dmitry131131/Trasser/img/1.jpg

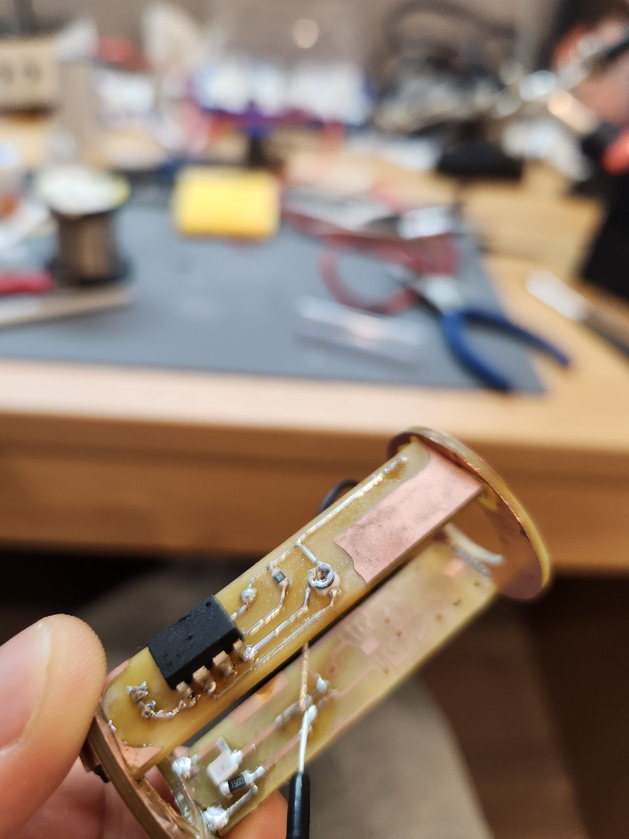
img/1.jpg
