dmitry131131/Trasser/img/2.jpg

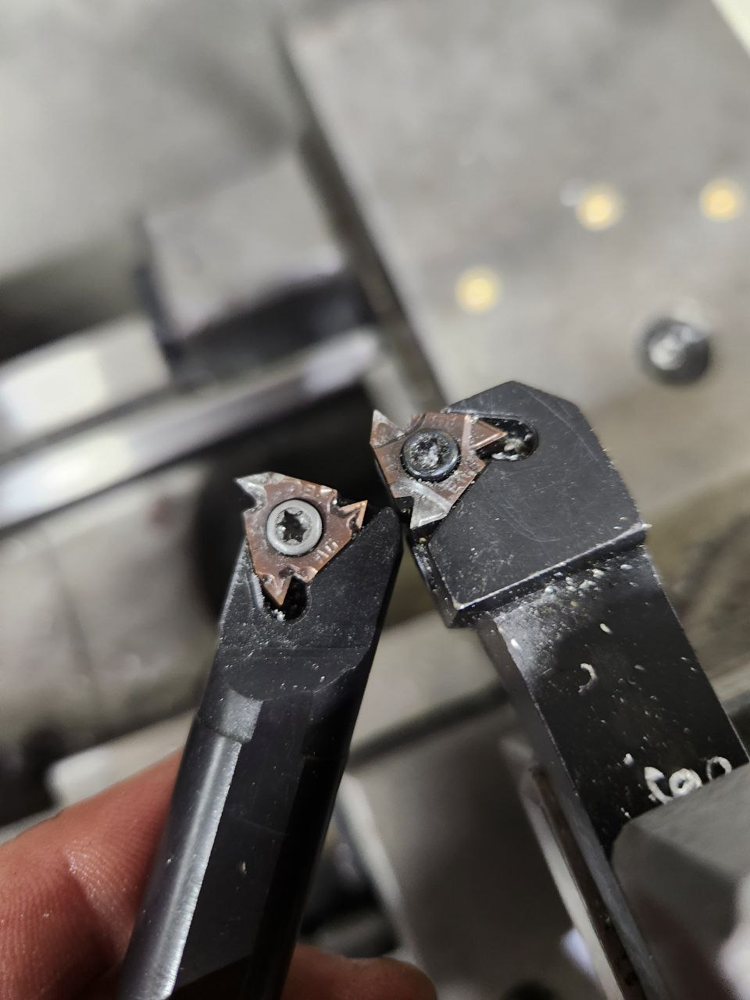
img/2.jpg
