dmitry131131/Trasser/img/3.jpg

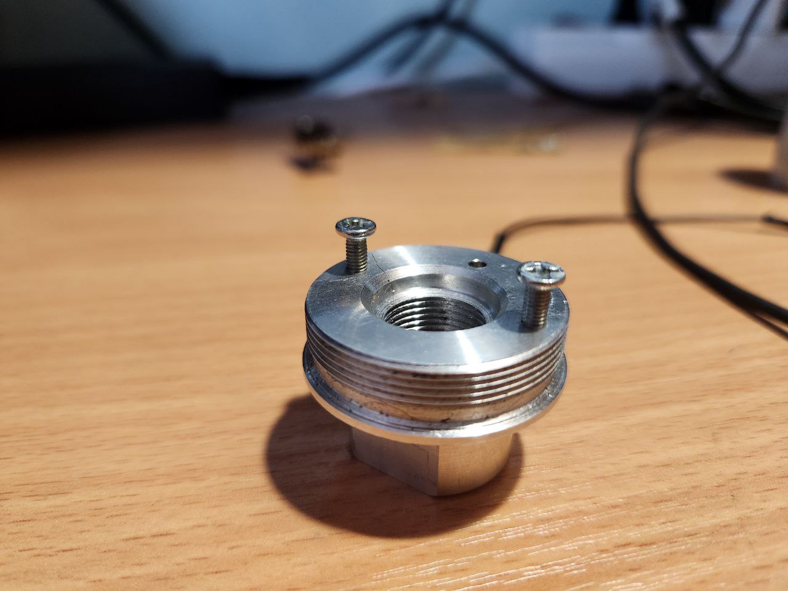
img/3.jpg
