dmitry131131/Trasser/img/Зад.PNG

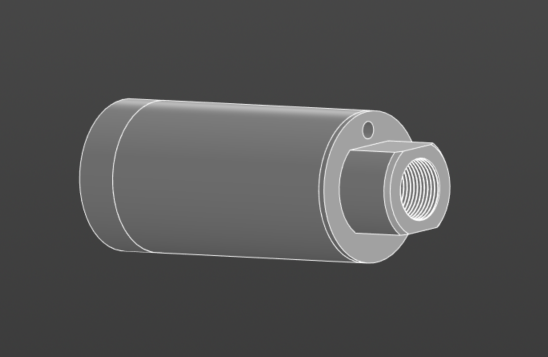
img/Зад.PNG
